kiwicon-badge/badge/lab-01/images/led01-breadboard.png

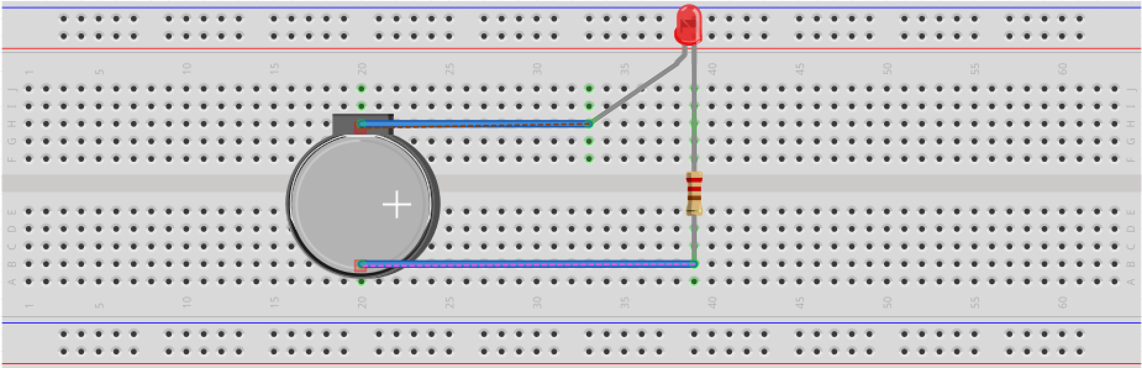
lab-01/images/led01-breadboard.png
