kiwicon-badge/badge/lab-01/images/led02-breadboard.png

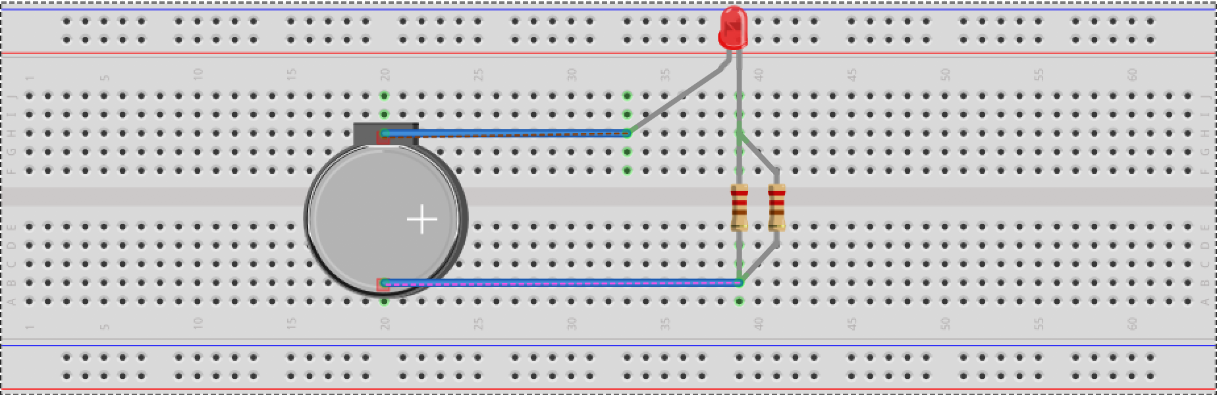
lab-01/images/led02-breadboard.png
