kiwicon-badge/badge/lab-01/images/led-breadboard.png

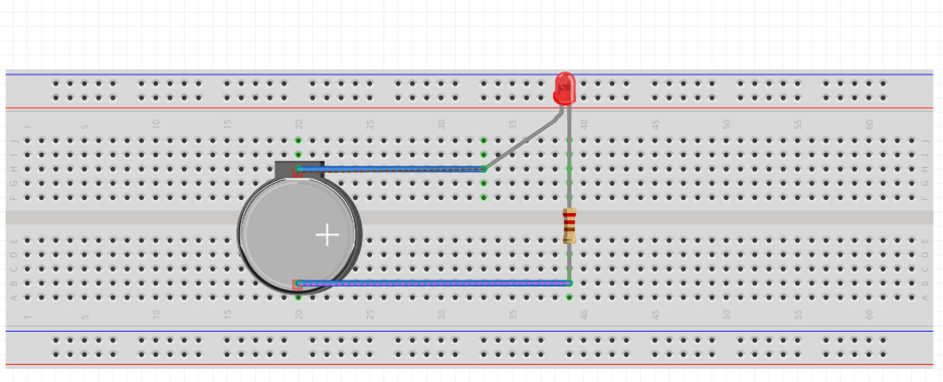
lab-01/images/led-breadboard.png
