kiwicon-badge/badge/lab-03/images/programmer.png

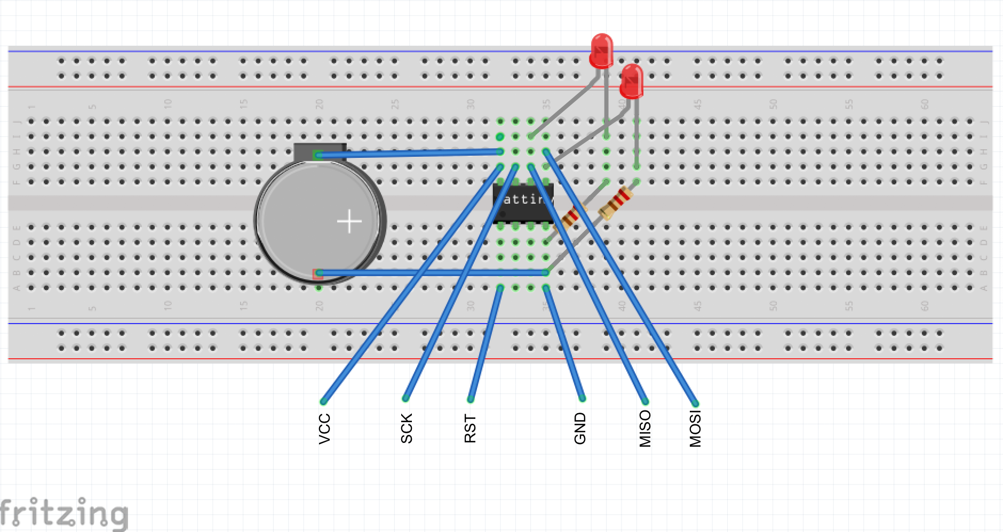
lab-03/images/programmer.png
